KylerM-23/Pico-Advent-Calendar/Templates/day9_Button_Matrix_template.py

from machine import Pin
import time

class Button_Matrix:
    matrix_pin_num = []
    matrix_pins_obj = []		#Pin Objects
    
    rows = 0
    cols = 0

    def __init__(self, pin_matrix):
        try:
            #
        except:
            raise Exception("Error in matrix formatting.")
        
        row_list = []
        col_list = []
        
        for row in range(self.rows):
            #
        
    def get_input(self, row, col):
        #
    
if __name__ == '__main__':    # Program entrance
    print ('Demo Code for Button Matrix')
    Buttons = Button_Matrix(pin_matrix = [[11,8], [12,13]])
    while True:
        time.sleep(1)
        for row in range(2):
            for col in range(2):
                print("Row", row, "Col", col, "Value:", Buttons.get_input(row, col))
        print()
